Makssse/Projet-Multidisciplinaire/src/code_salles/code salle 2/lib_IP_MAC.py

import network
from machine import Pin, SPI
import time

def connect_ethernet():
    # Force le reset matériel
    eth_reset = Pin(20, Pin.OUT)
    eth_reset.value(0) # On éteint la puce
    time.sleep(0.1)
    eth_reset.value(1) # On la rallume
    time.sleep(0.5)    # On attend qu'elle finisse de booter

    # Configuration SPI (On peut monter à 20MHz pour plus de perf)
    spi = SPI(0, 20_000_000, mosi=Pin(19), miso=Pin(16), sck=Pin(18))
    
    # Initialisation du contrôleur WIZNET5K
    # CS=17, Reset=20 (géré manuellement au dessus), mais on le passe au driver
    nic = network.WIZNET5K(spi, Pin(17), Pin(20)) 
    
    nic.active(True)
    
    # Affichage de la MAC pour vérification
    import ubinascii
    mac = ubinascii.hexlify(nic.config('mac'),':').decode()

    timeout = 150
    while not nic.isconnected() and timeout > 0:
        # On vérifie l'état du lien physique (0: pas de câble, 1: câble ok)
        status = nic.status() 
        time.sleep(1)
        timeout -= 1
    ip = nic.ifconfig()[0]
    return mac, ip
