Makssse/Projet-Multidisciplinaire/src/code_salles/code salle 2/lib_led.py

import machine
import time
from Led import *

# --- CONFIGURATION ---
def config_led(NUM_LEDS,PIN_DATA,PIN_CLOCK,BRIGHTNESS):
    LED_STRIP = DotStar(PIN_DATA, PIN_CLOCK, NUM_LEDS, BRIGHTNESS)
    return LED_STRIP

def indicateur_visuel(CO2_ppm,bandeau, SEUIL_CO2_OK, SEUIL_CO2_ALERTE):
    if CO2_ppm<SEUIL_CO2_OK:
        bandeau.fill(0,255,0)
    
    if SEUIL_CO2_OK<=CO2_ppm<=SEUIL_CO2_ALERTE:
        bandeau.fill(255, 80, 0) 

    if CO2_ppm>SEUIL_CO2_ALERTE:
        bandeau.fill(255,0,0)

def piloter_led(etat, bandeau):
    if etat == 1:
        bandeau.fill(255,255,255)
    if etat == 0:
        bandeau.fill(0,0,0)
